JavierIH/miniKame/doc/images/foot.png

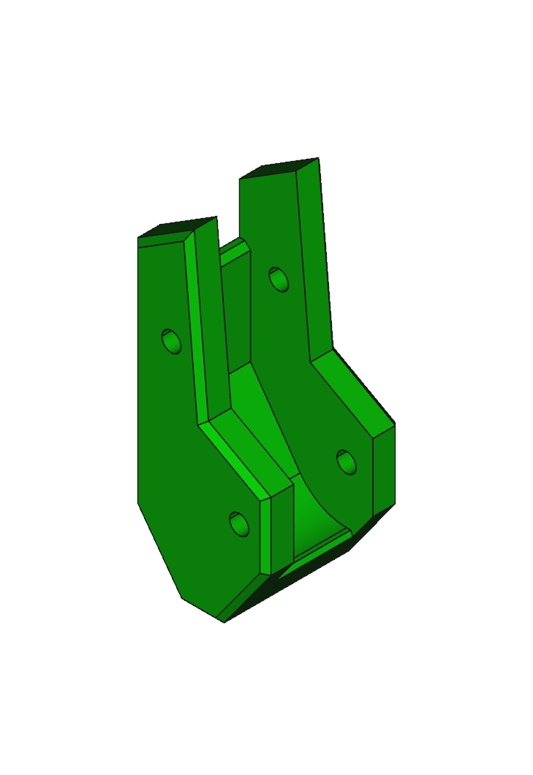
doc/images/foot.png
