JavierIH/miniKame/doc/images/legA.png

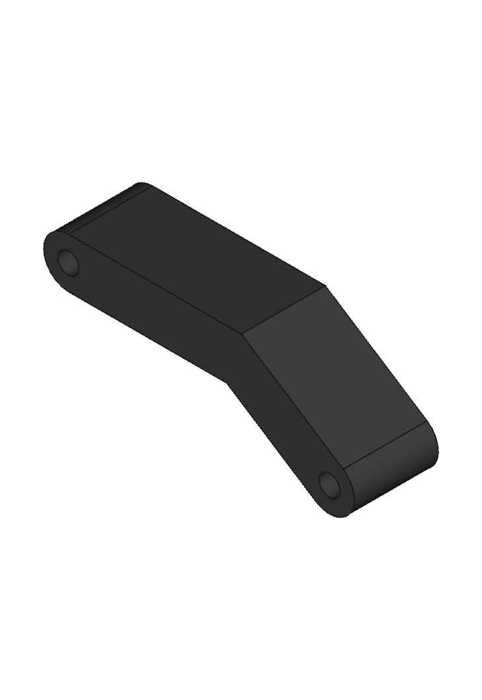
doc/images/legA.png
