JavierIH/miniKame/doc/images/main.png

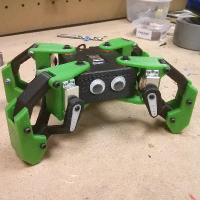
doc/images/main.png
