JavierIH/miniKame/doc/images/rightBracket.png

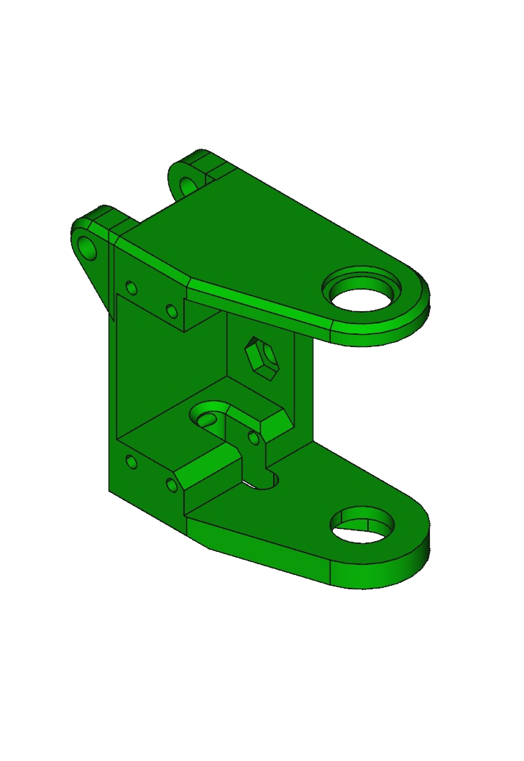
doc/images/rightBracket.png
